tianxiaogua/wheel_robot/hardware/board-foc/V0.5/foc_driver-V0.5.pdf

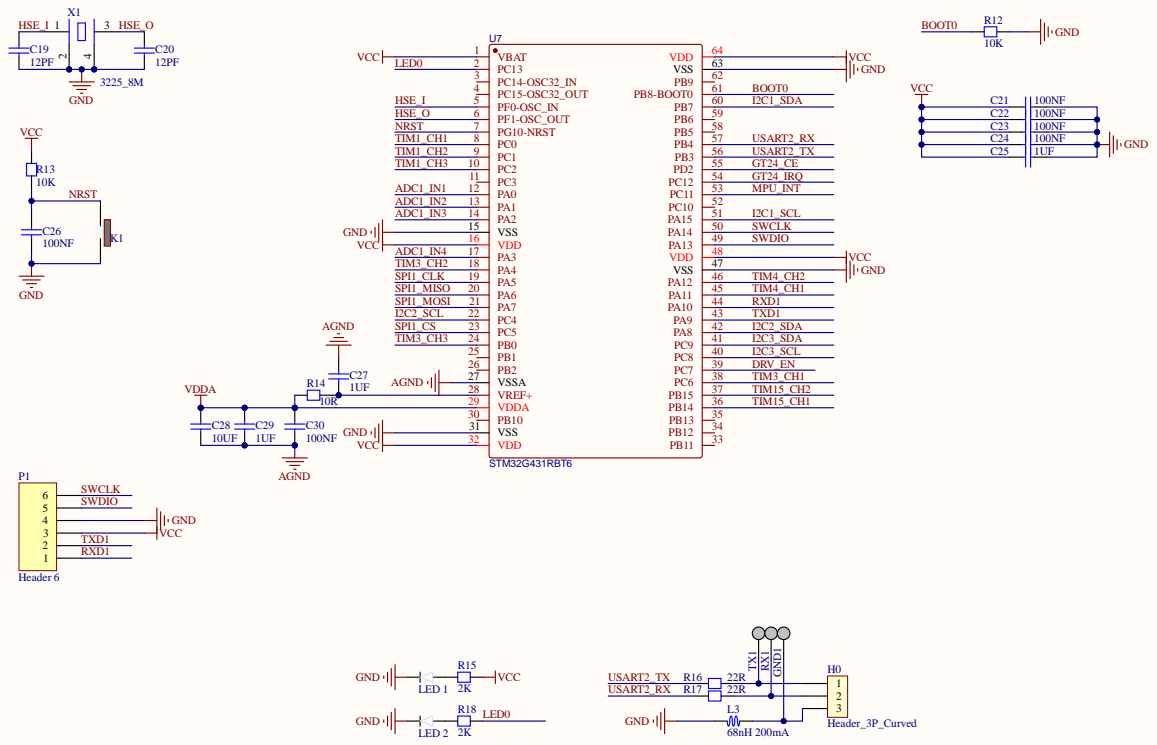
[picture p11: page 1]

C22 | 100N | F
C23 | 100N | F
C24 | 100N | F

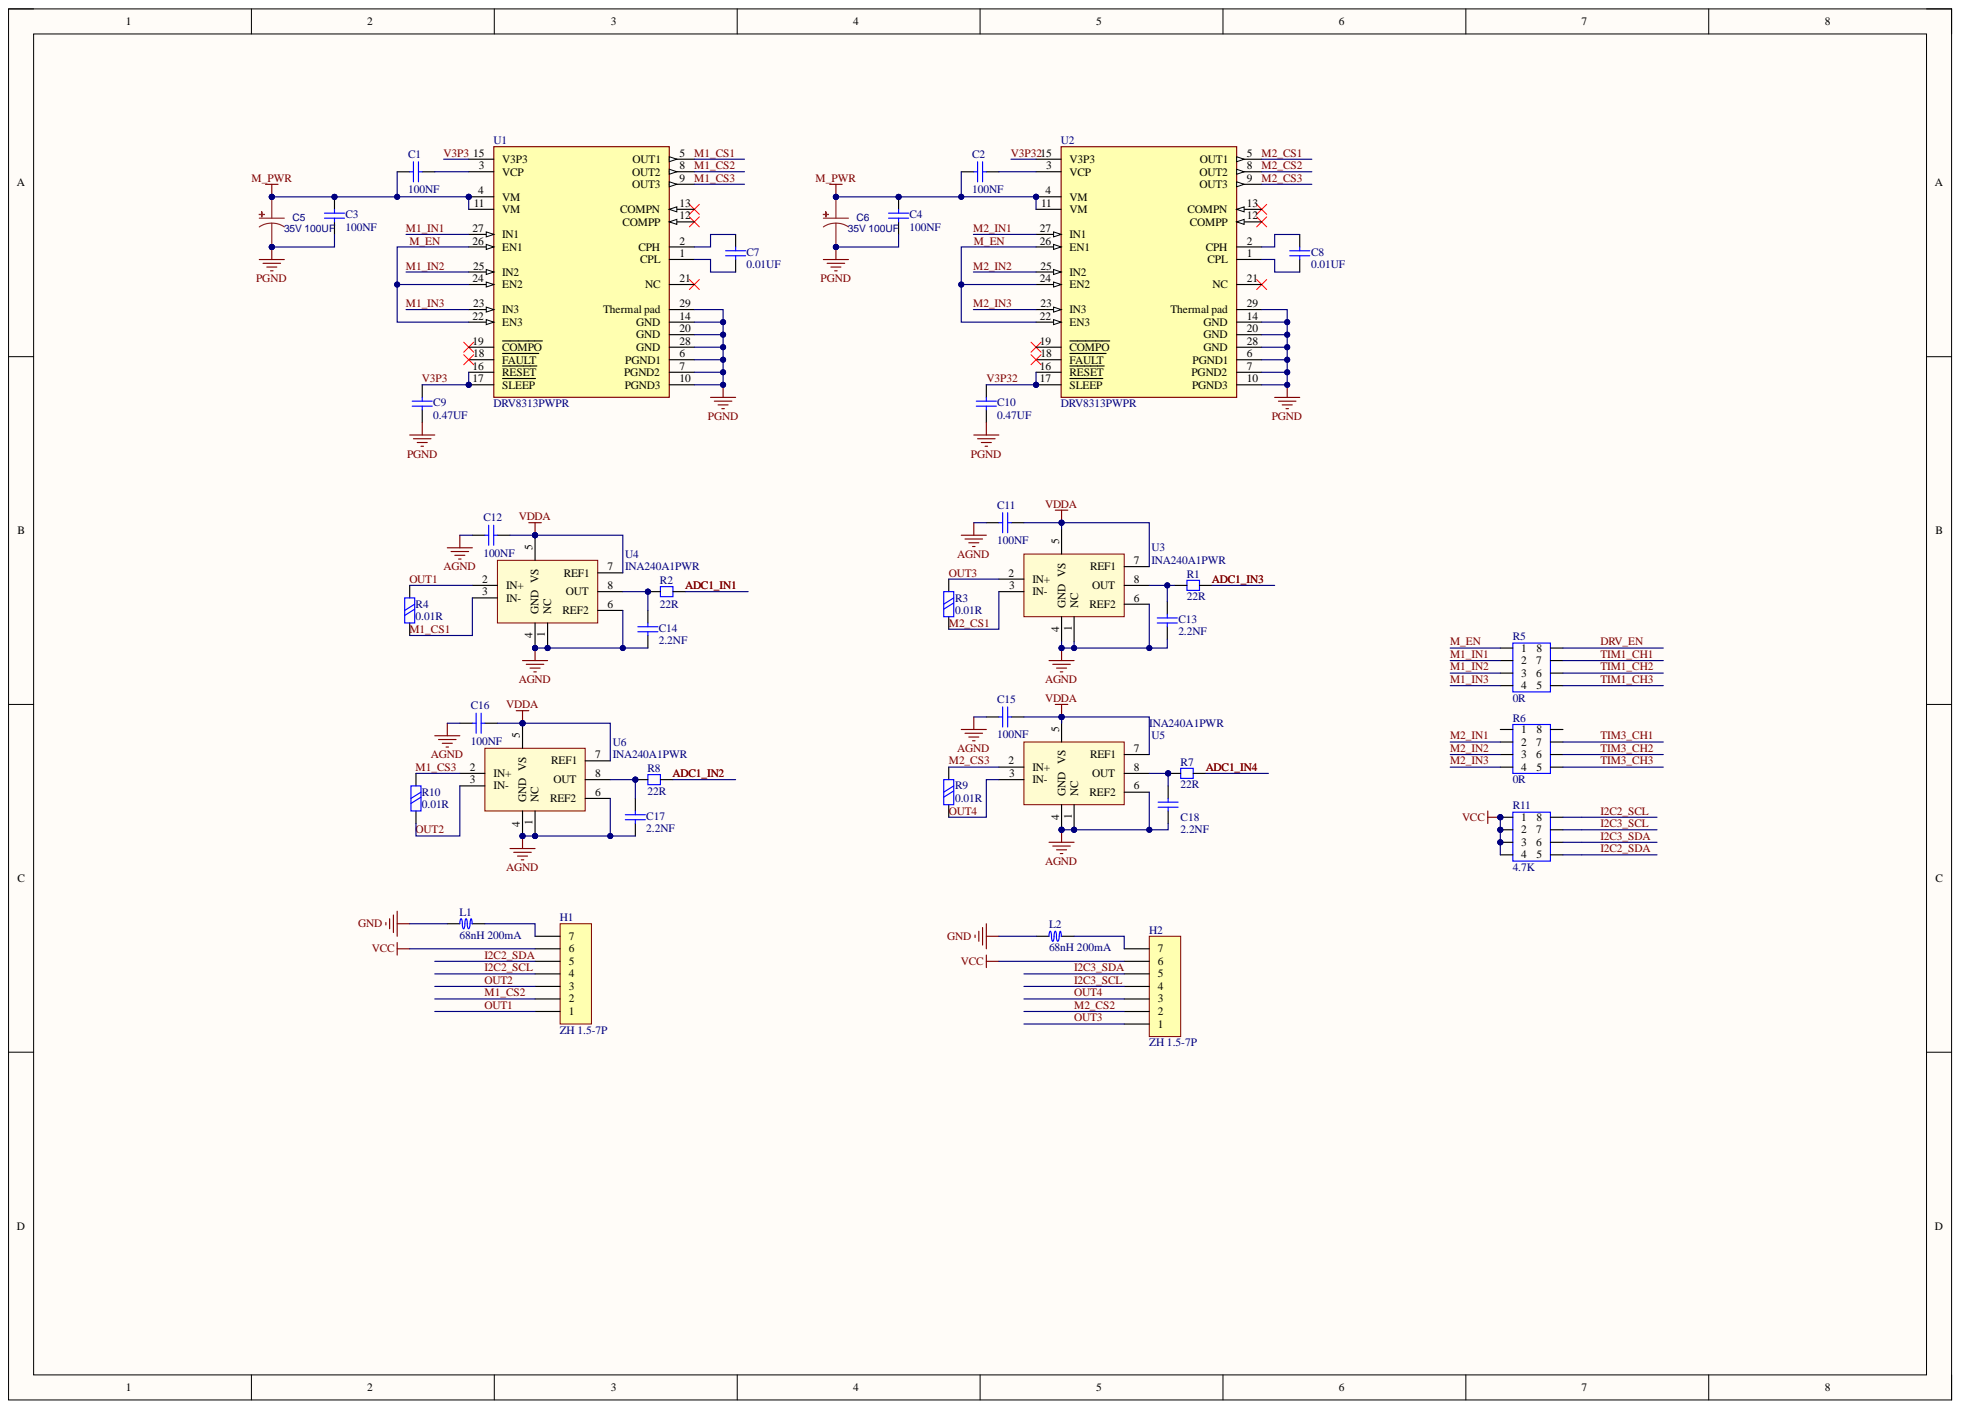
[picture p12: page 2]

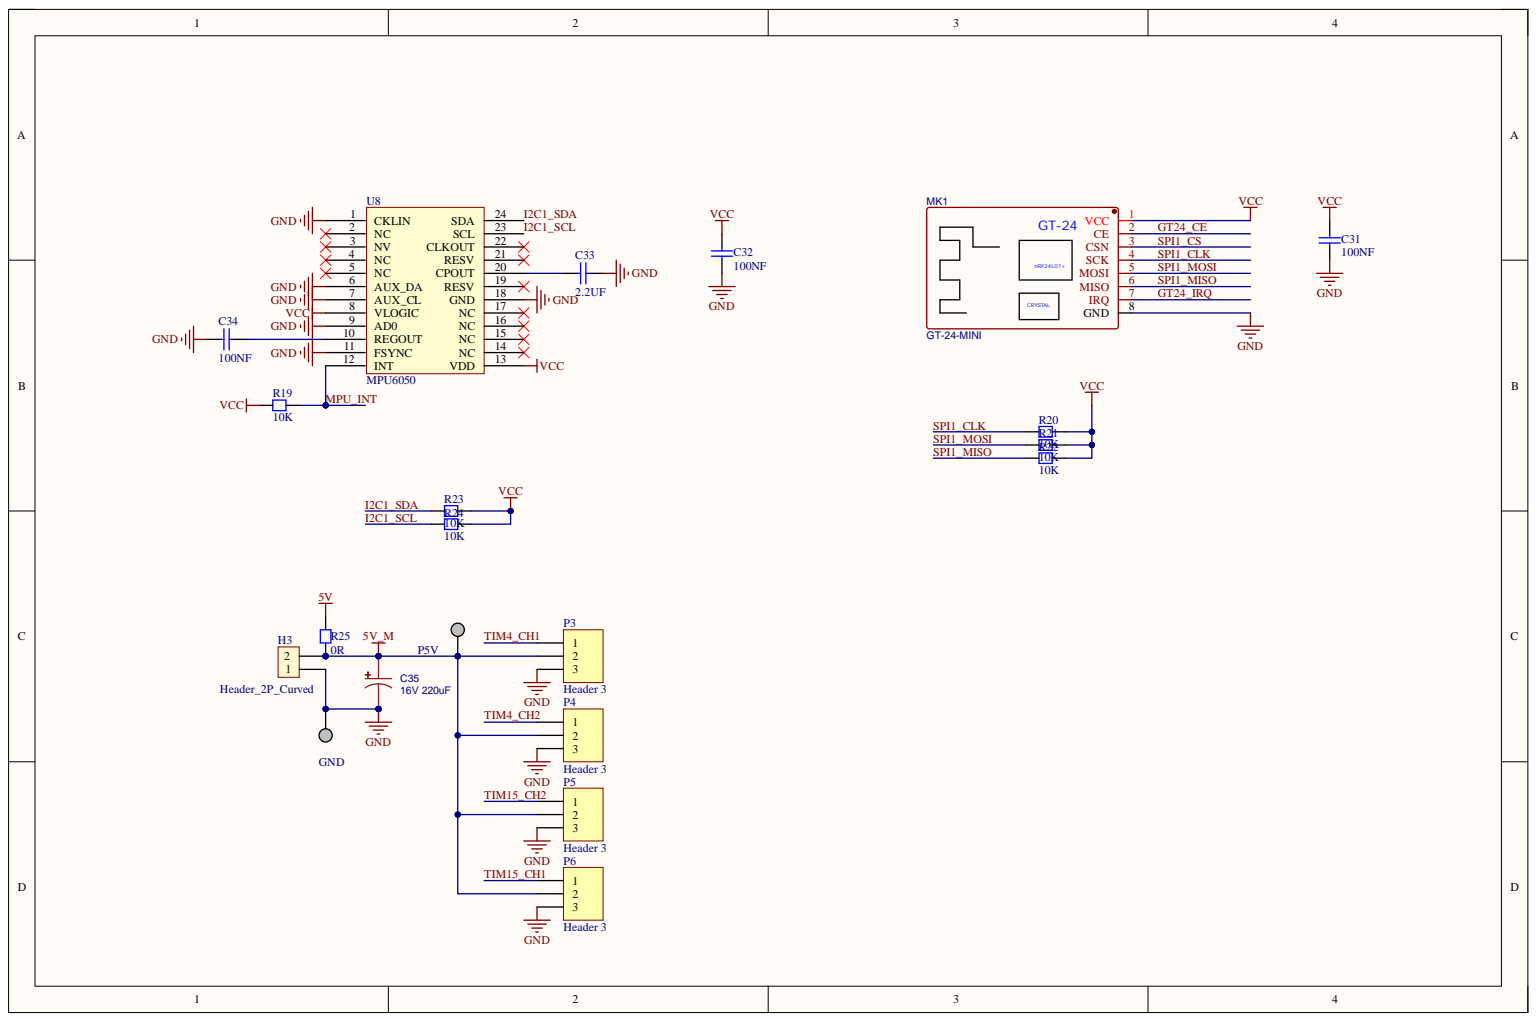
[picture p13: page 3]

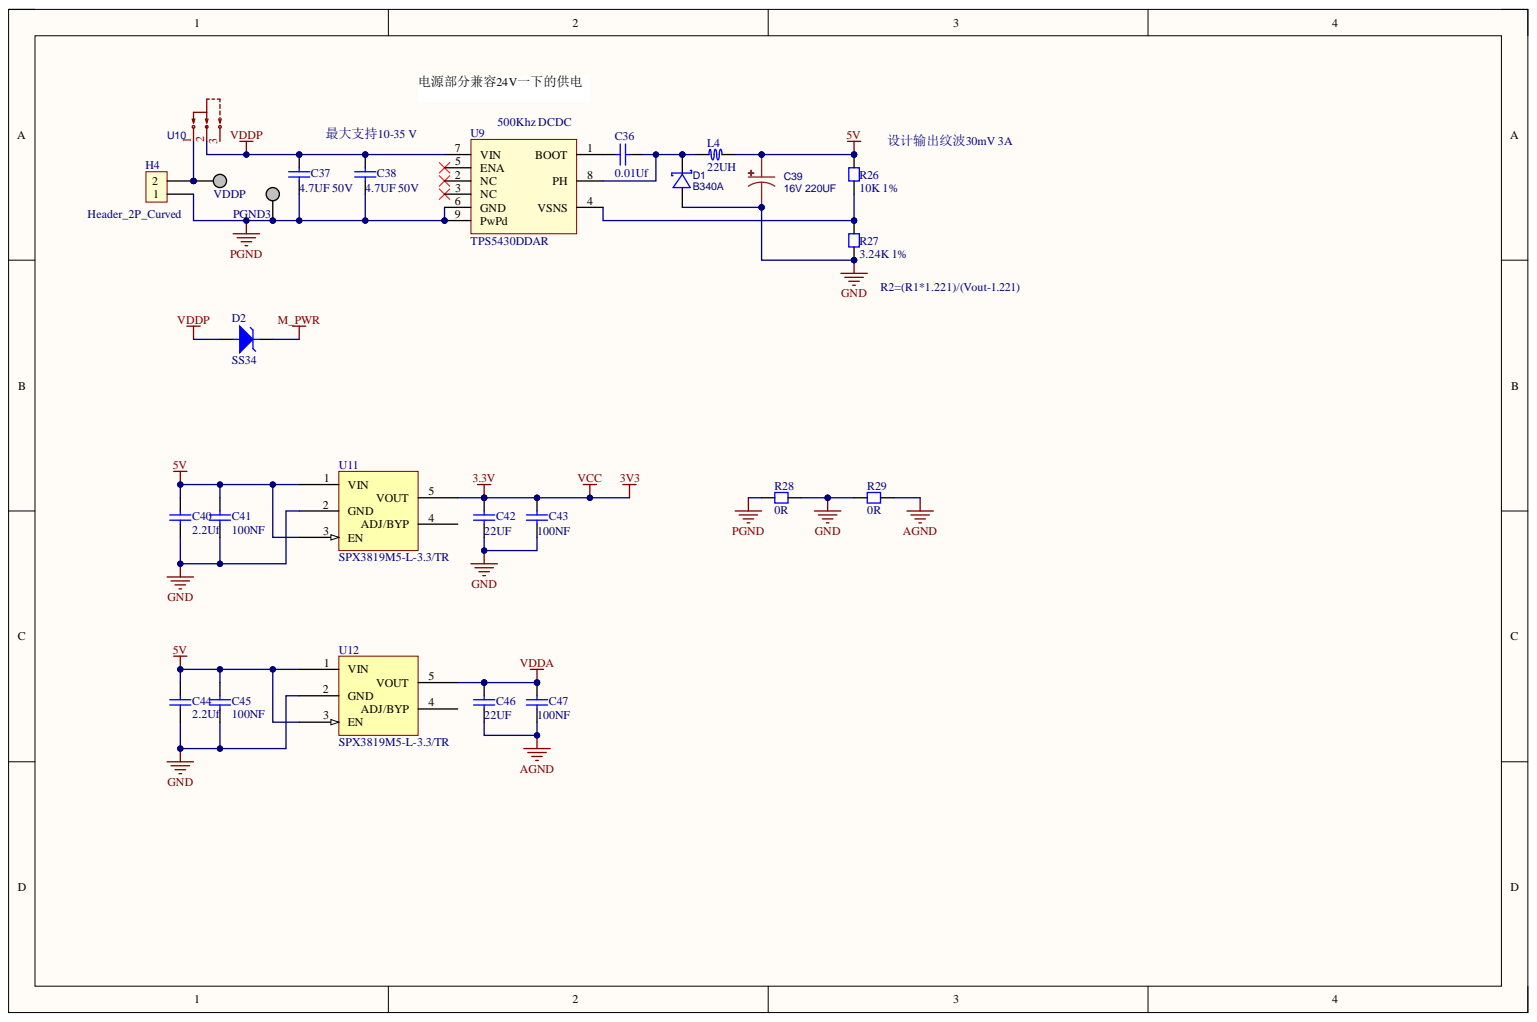
[picture p14: page 4]

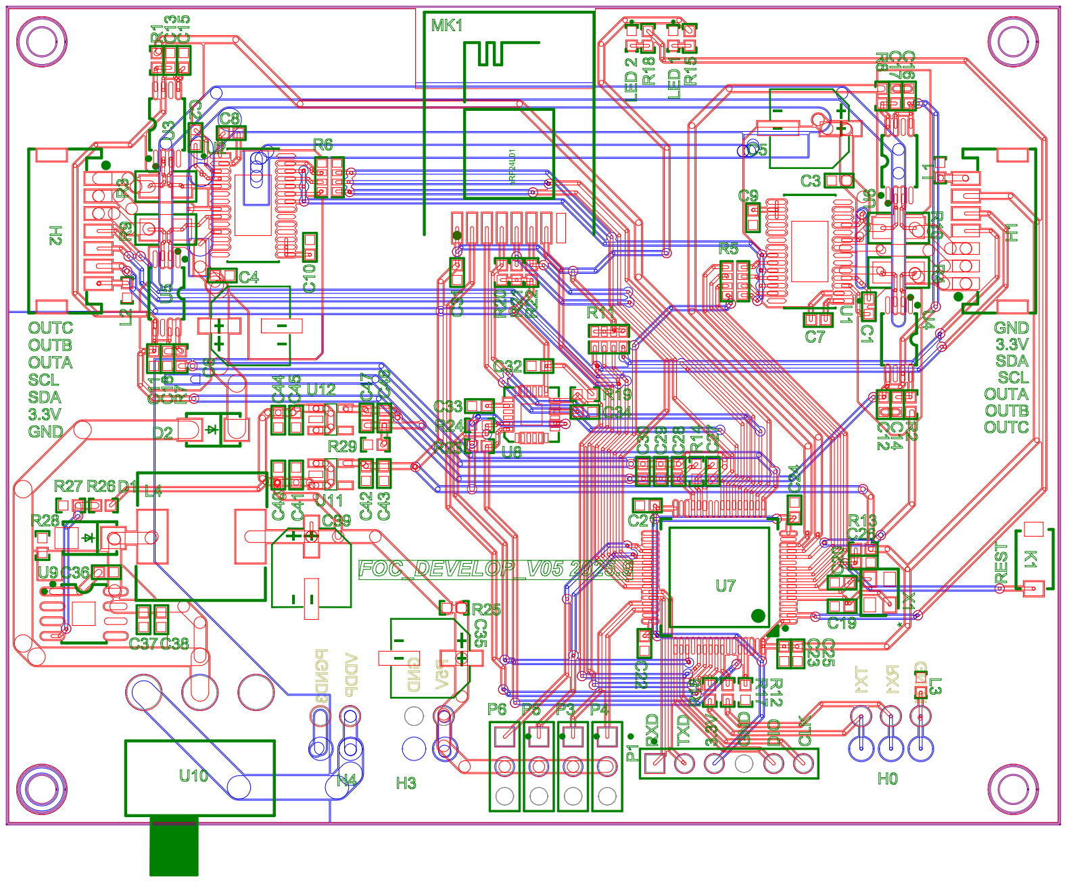
[picture p15: page 5]
