tianxiaogua/wheel_robot/hardware/board-foc/V0.4/foc_driver-V0.4.pdf

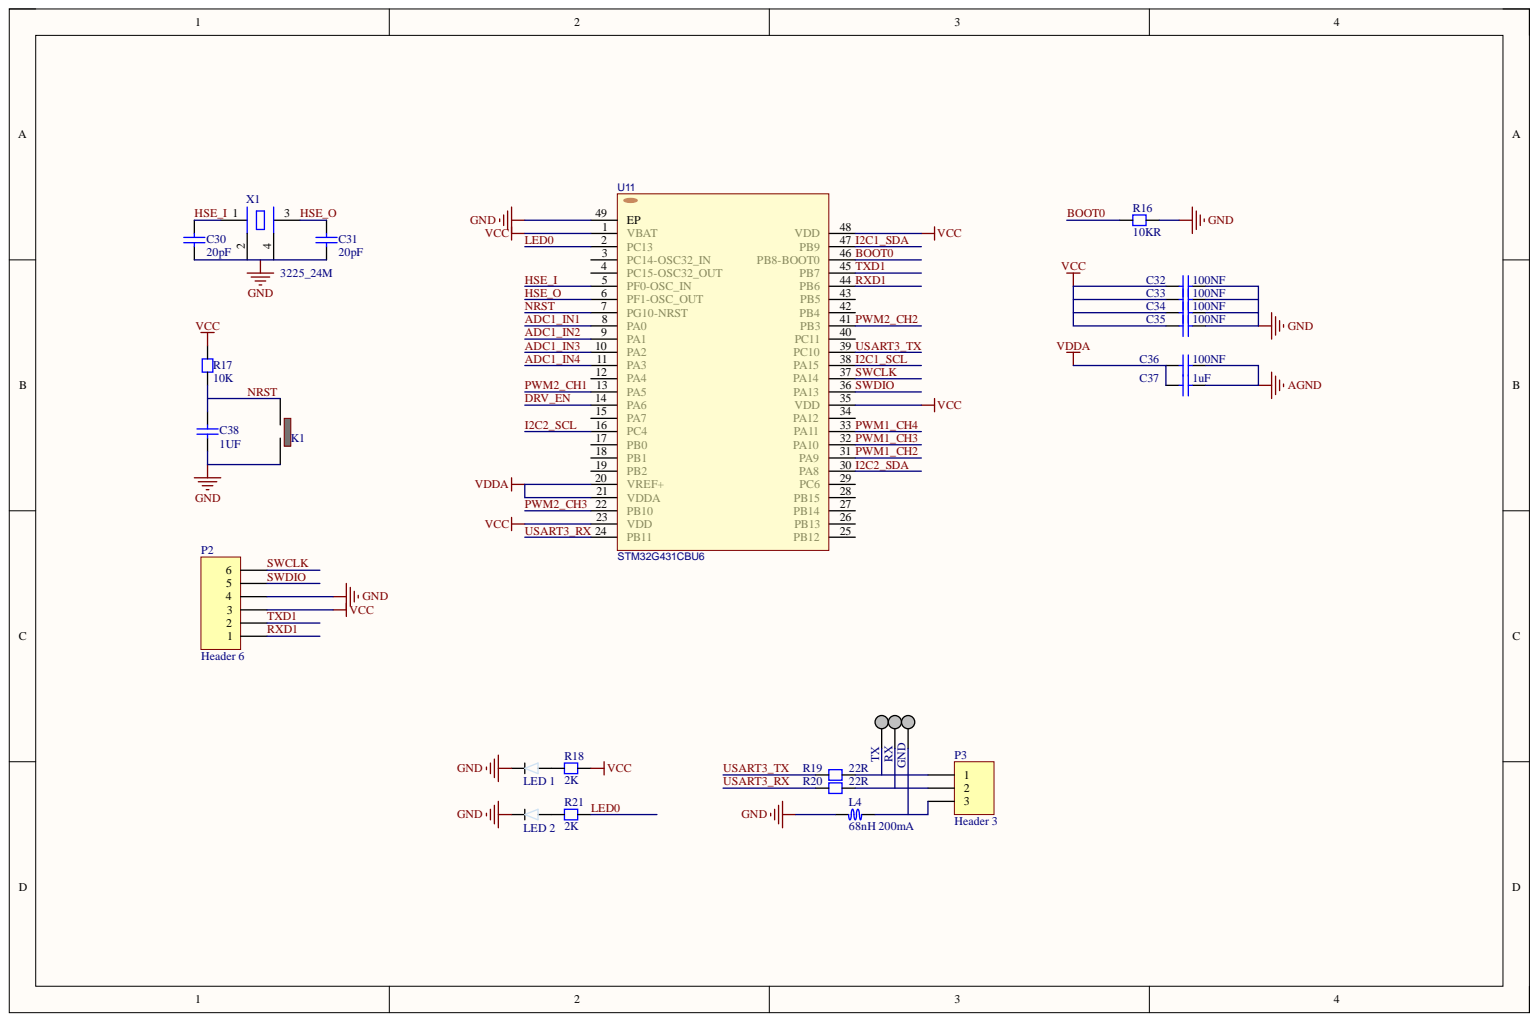
[picture p16: page 1]

C3 3 | 1 0 | 0 N F
C3 4 | 1 0 | 0 N F
C3 5 | 1 0 | 0 N F

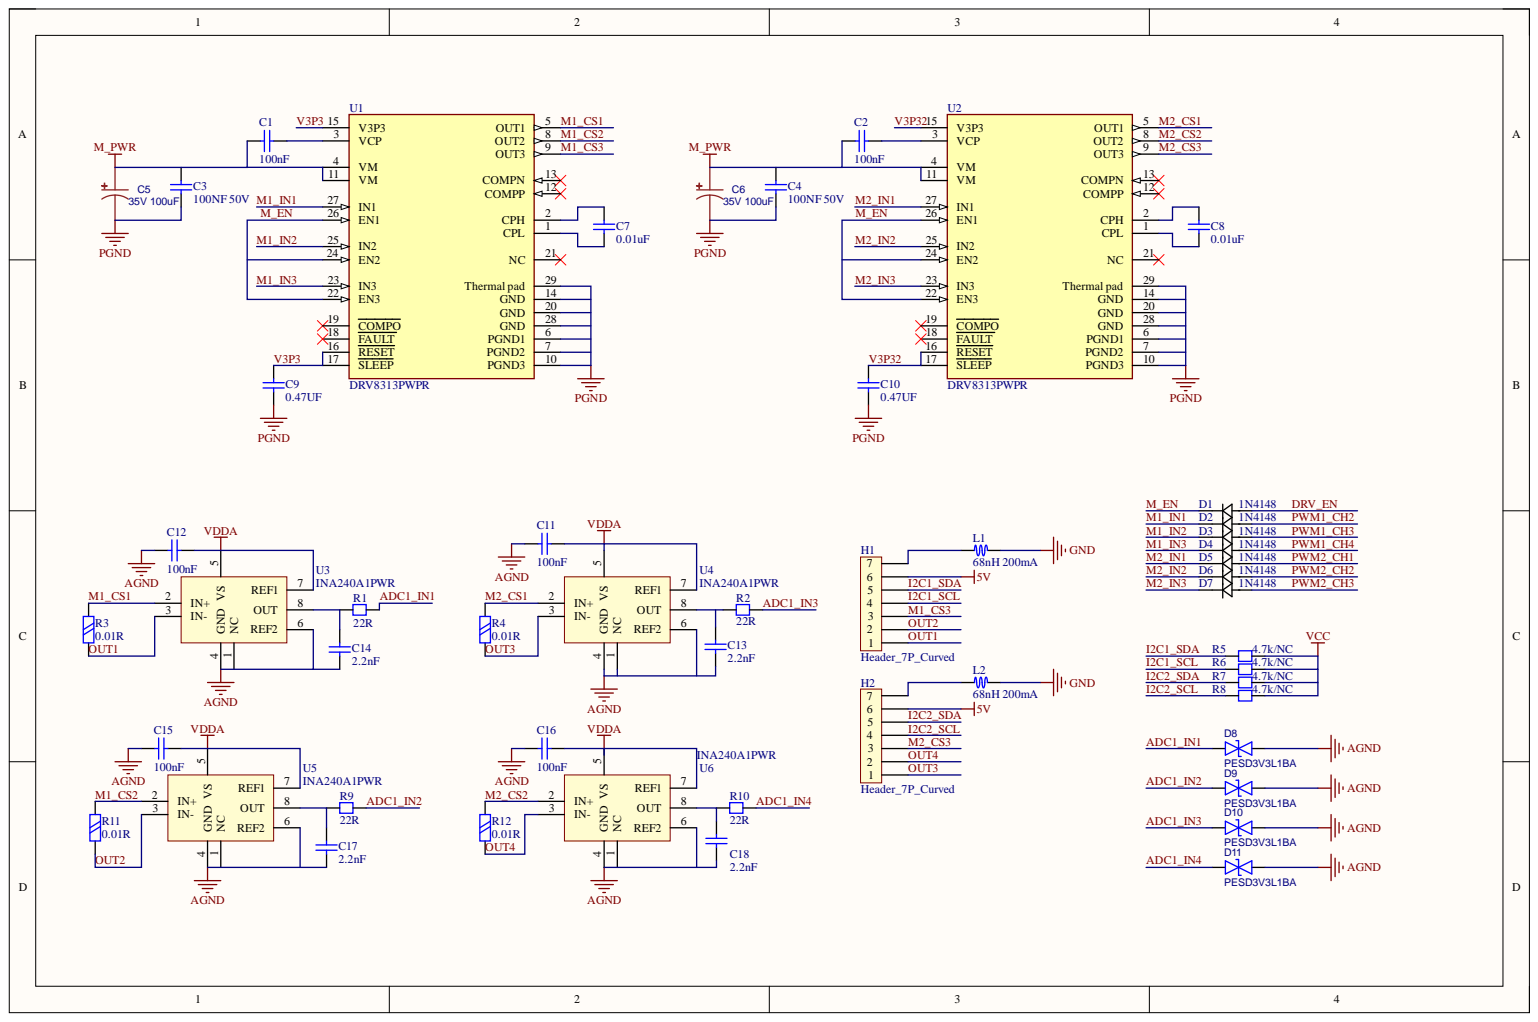
[picture p17: page 2]

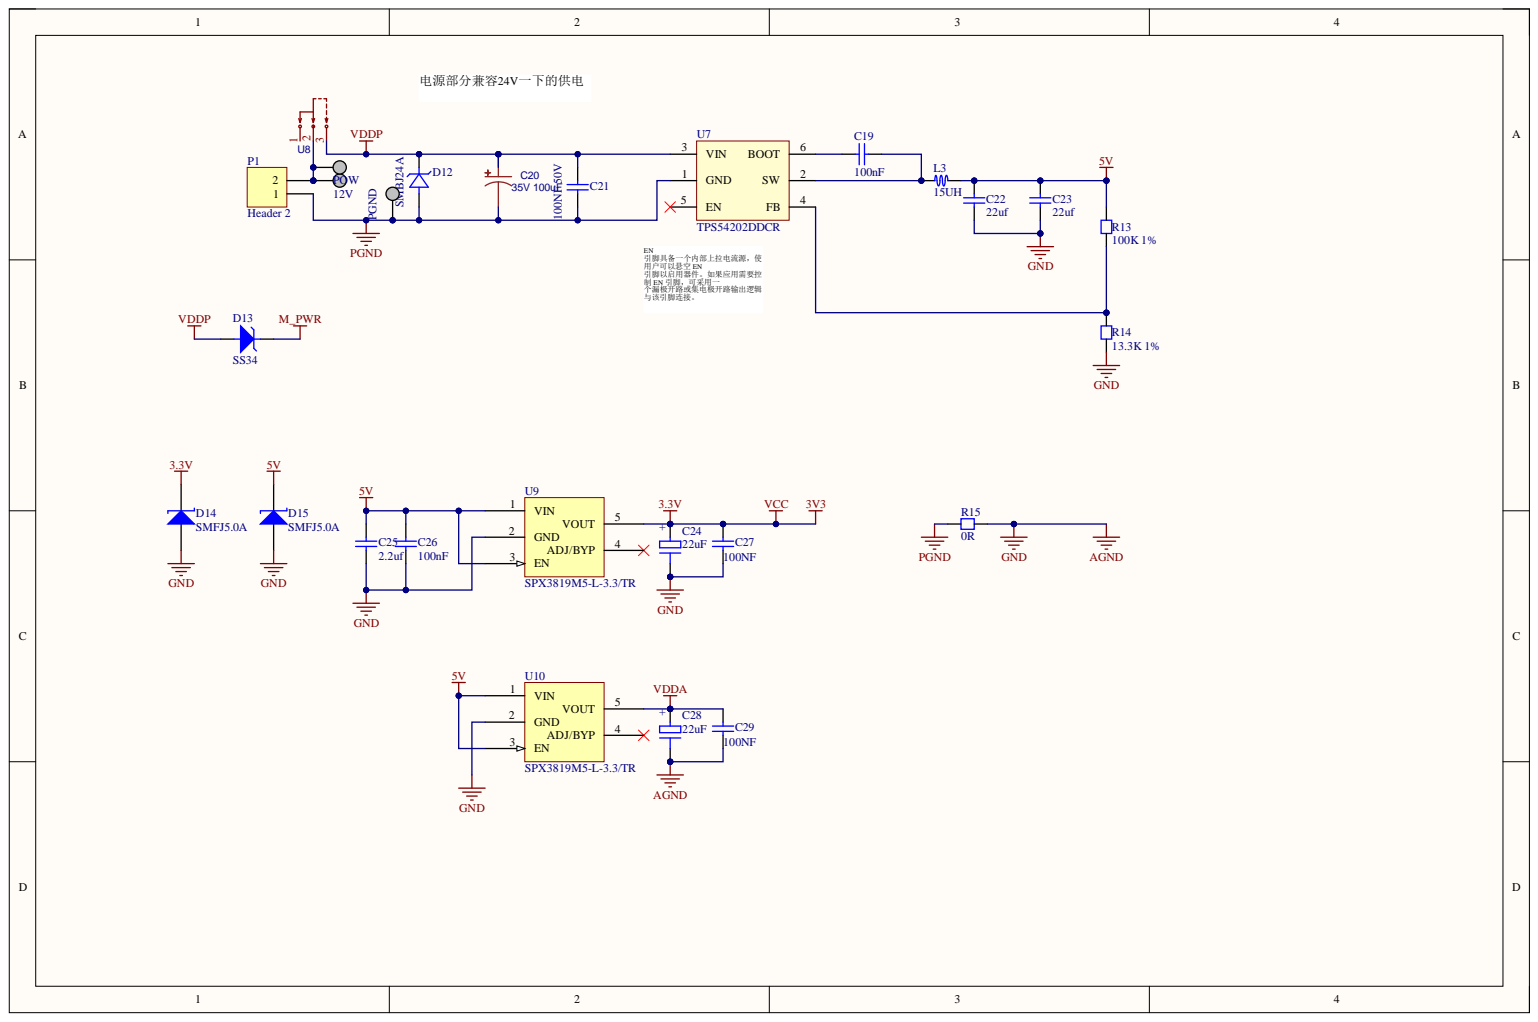
[picture p18: page 3]

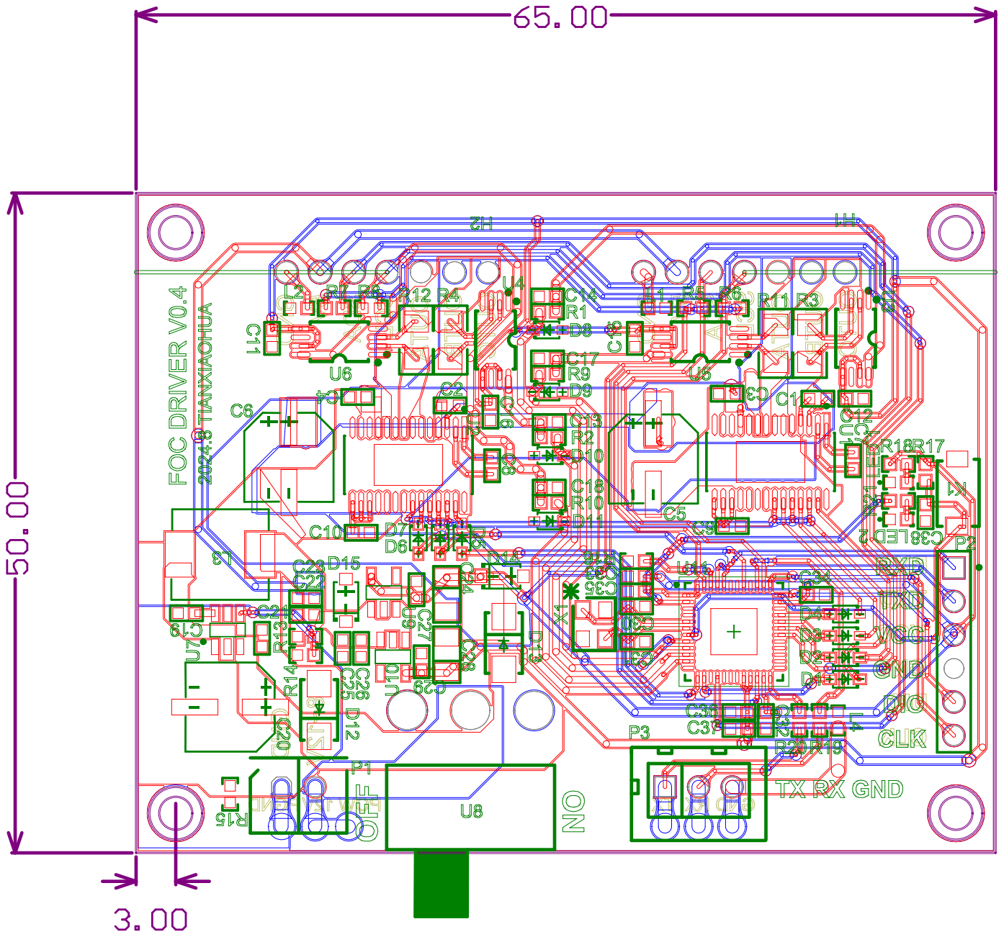
[picture p19: page 4]
