tianxiaogua/wheel_robot/singlechip/app/MCU_device/nvic_device.c

#include "nvic_device.h"
//#include "foc.h"
#include "as5600.h"
#include "stdio.h"
#include "usart_device.h"
#include "adc_device.h"
#include "BLDCMotor.h"
#include "FOCMotor.h"
#include "BLDCMotor.h"
#include "MagneticSensor.h"
#include "app.h"

typedef struct
{
  nvic_callback callback_fun;
} NVIC_CTX;

NVIC_CTX g_nvic_ctx = {0};

void nvic_register_callback(nvic_callback fun)
{
  if (fun == NULL) {
    printf("eeor!\r\n");
  }
  g_nvic_ctx.callback_fun = fun;
}


/*******************************************************************************
 * @file   : vnic_device.c
 * @brief  : 启动中断
 * @author : tianxiaohua
 * @date   : 2023-04
 ******************************************************************************/
void start_interrupt(void)
{

#if  FOC_CURRENT_LOOP
  HAL_TIM_Base_Start_IT(&htim7); // main loop interrupt
  HAL_TIM_Base_Start_IT(&htim1); // gat adc timer
  HAL_TIM_Base_Start_IT(&htim5); // main loop interrupt
  HAL_TIM_Base_Start_IT(&htim2); // speed feedback
#else
  HAL_TIM_Base_Start_IT(&htim2); // speed feedback  20Hz
#endif
}


/*******************************************************************************
 * @file   : vnic_device.c
 * @brief  : 设置定时器的中断2ms一次，定时器中断函数 在50ms 20Hz一次的中断内 通过计数的方式分频出50、100、200、500ms
定时时间： Time = (ARR+1) * (PSC+1) / Tclk = （重装载值+1）（预分频系数+1）/ 时钟频率 = （7199+1） （9999+1）/ 72 000 000 = 1s
 * @author : tianxiaohua
 * @date   : 2023-04
 ******************************************************************************/
uint32_t time_flag = 0;
float history_L_Mspeed = 0;
float history_R_Mspeed = 0;
void HAL_TIM_PeriodElapsedCallback(TIM_HandleTypeDef *htim)
{
  if(htim == &htim2)  // htim2 被设置为1毫秒中断一次
  {
    g_nvic_ctx.callback_fun();
  }
}
